PROTONMM/YR-PCB-v0.4/img/20251109_183437.jpg

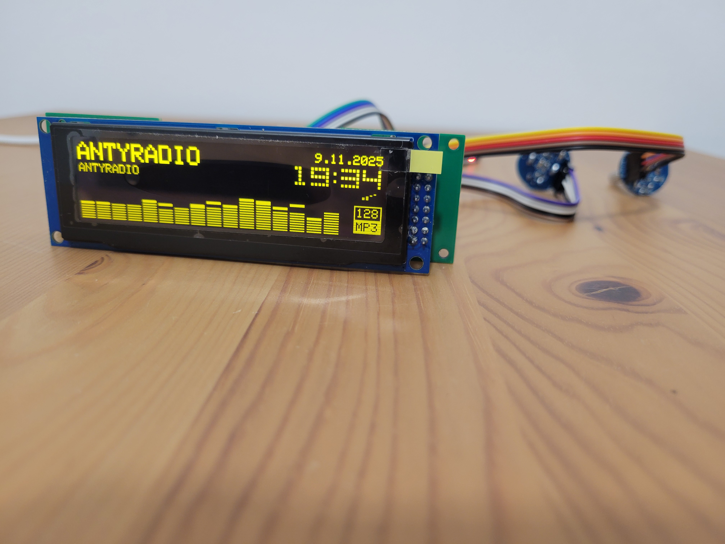
img/20251109_183437.jpg
